sparkfun/ESP32_Motion_Shield/Software/BME280_I2C_SPI/BME280_I2C_SPI.ino

/******************************************************************************
BME280_I2C_SPI.ino
BME280 on the ESP32 Thing

Marshall Taylor @ SparkFun Electronics
Original creation date: May 20, 2015
Modified: Nov 6, 2017
https://github.com/sparkfun/ESP32_Motion_Shield

This sketch configures a BME280 to produce comma separated values for use
in generating spreadsheet graphs.

It has been modified from the original BME280 example to demonstrate I2C and
SPI operation on the ESP32 Motion board.

Original source:
https://github.com/sparkfun/SparkFun_BME280_Arduino_Library

Resources:
Uses Wire.h for I2C operation
Uses SPI.h for SPI operation

Development environment specifics:
Arduino IDE 1.8.2

This code is released under the [MIT License](http://opensource.org/licenses/MIT).
Please review the LICENSE.md file included with this example. If you have any questions 
or concerns with licensing, please contact techsupport@sparkfun.com.
Distributed as-is; no warranty is given.
******************************************************************************/
#include <stdint.h>
#include "SparkFunBME280.h"

#include "Wire.h"
#include "SPI.h"


//Global sensor object
BME280 mySensor;

unsigned int sampleNumber = 0; //For counting number of CSV rows

void setup()
{
	Wire.begin();
			
	// For SPI, enable the "mySensor.beginSPI(10)" line and disable the "mySensor.beginI2C()" line.
  if (mySensor.beginI2C() == false) //Begin communication over I2C.
  //if (mySensor.beginSPI(17) == false) //Begin communication over SPI. Use pin 17 as Chip Select.
  {
    Serial.println("The sensor did not respond. Please check wiring.");
    while(1); //Freeze
  }


	//***BME280 Operation settings*****************************//
	mySensor.setFilter(1); //0 to 4 is valid. Filter coefficient. See 3.4.4
  mySensor.setStandbyTime(0); //0 to 7 valid. Time between readings. See table 27.

  mySensor.setTempOverSample(1); //0 to 16 are valid. 0 disables temp sensing. See table 24.
  mySensor.setPressureOverSample(1); //0 to 16 are valid. 0 disables pressure sensing. See table 23.
  mySensor.setHumidityOverSample(1); //0 to 16 are valid. 0 disables humidity sensing. See table 19.
  
  mySensor.setMode(MODE_NORMAL); //MODE_SLEEP, MODE_FORCED, MODE_NORMAL is valid. See 3.3
	
	Serial.begin(115200);
	Serial.print("Program Started\n");
	Serial.print("Starting BME280... result of .begin(): 0x");
	delay(10);  //Make sure sensor had enough time to turn on. BME280 requires 2ms to start up.
	//Calling .begin() causes the settings to be loaded
	Serial.println(mySensor.begin(), HEX);

	//Build a first-row of column headers
	Serial.print("\n\n");
	Serial.print("Sample,");
	Serial.print("T(deg C),");
	Serial.print("T(deg F),");
	Serial.print("P(Pa),");
	Serial.print("Alt(m),");
	Serial.print("Alt(ft),");
	Serial.print("%RH");
	Serial.println("");
	
}

void loop()
{

	//Print each row in the loop
	//Start with temperature, as that data is needed for accurate compensation.
	//Reading the temperature updates the compensators of the other functions
	//in the background.
	Serial.print(sampleNumber);
	Serial.print(",");
	Serial.print(mySensor.readTempC(), 2);
	Serial.print(",");
	Serial.print(mySensor.readTempF(), 3);
	Serial.print(",");
	Serial.print(mySensor.readFloatPressure(), 0);
	Serial.print(",");
	Serial.print(mySensor.readFloatAltitudeMeters(), 3);
	Serial.print(",");
	Serial.print(mySensor.readFloatAltitudeFeet(), 3);
	Serial.print(",");
	Serial.print(mySensor.readFloatHumidity(), 0);
	Serial.println();
	
	sampleNumber++;
	
	delay(50);

}
