sparkfun/ESP32_Motion_Shield/Software/TestPrograms/Serial2LoopBack/Serial2LoopBack.ino

#include <Arduino.h>

HardwareSerial GPSUART(2);  // Setting up GPS UART1 on pins 16 & 17

#define AUX_LED_PIN 13

void setup(){
	pinMode(AUX_LED_PIN, OUTPUT);

    Serial.begin(115200);
	GPSUART.begin(9600);
	
	delay(1000);
	Serial.println("Starting Sketch.");
	Serial.println("Loopback GPS pins, then enter serial characters.");
	Serial.println("Test JST by installing GPS receiver.");
	digitalWrite(AUX_LED_PIN, 1);
	
}
int toggler = 0;

void loop(){
	char c;
	if(Serial.available())
	{
		c = Serial.read();
		GPSUART.print(c);
		digitalWrite(AUX_LED_PIN, toggler);
		toggler ^= 0x01;
	}
	if(GPSUART.available())
	{
		c = GPSUART.read();
		Serial.print(c);
	}
	delay(10);
}
